NeLaurynas/PicoRC2/tank/src/hooks.h

// Copyright (C) 2026 Laurynas 'Deviltry' Ekekeke
// SPDX-License-Identifier: BSD-3-Clause

#pragma once

#include <FreeRTOS.h>
#include <task.h>

void vApplicationStackOverflowHook(TaskHandle_t task, char *task_name);
void vApplicationMallocFailedHook();
